Jannled/SmartScale2/src/Constants.hpp

/**
 * @author Jannik Schmöle (@Jannled)
 * @date 2026-05-08
 */

#ifndef SMARTSCALE_CONSTANTS_H
#define SMARTSCALE_CONSTANTS_H

#define HAS_TOPIC_CONFIG "/config"
#define HAS_TOPIC_SET "/set"
#define HAS_TOPIC_STATE "/state"

#endif // SMARTSCALE_CONSTANTS_H
